tbtaco/Senior-Design/EAGLE/Batch 1/Button Board/Button Board Back.png

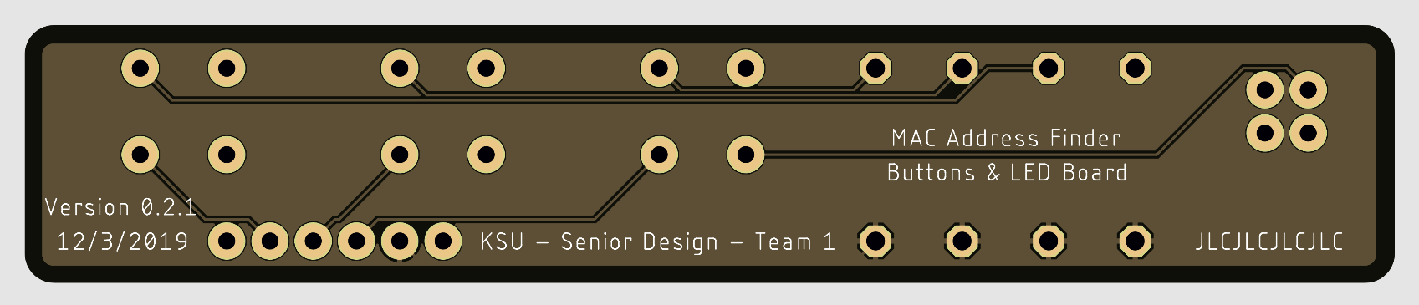
EAGLE/Batch 1/Button Board/Button Board Back.png
