tbtaco/Senior-Design/EAGLE/Batch 1/Button Board/Button Board BRD Dark.png

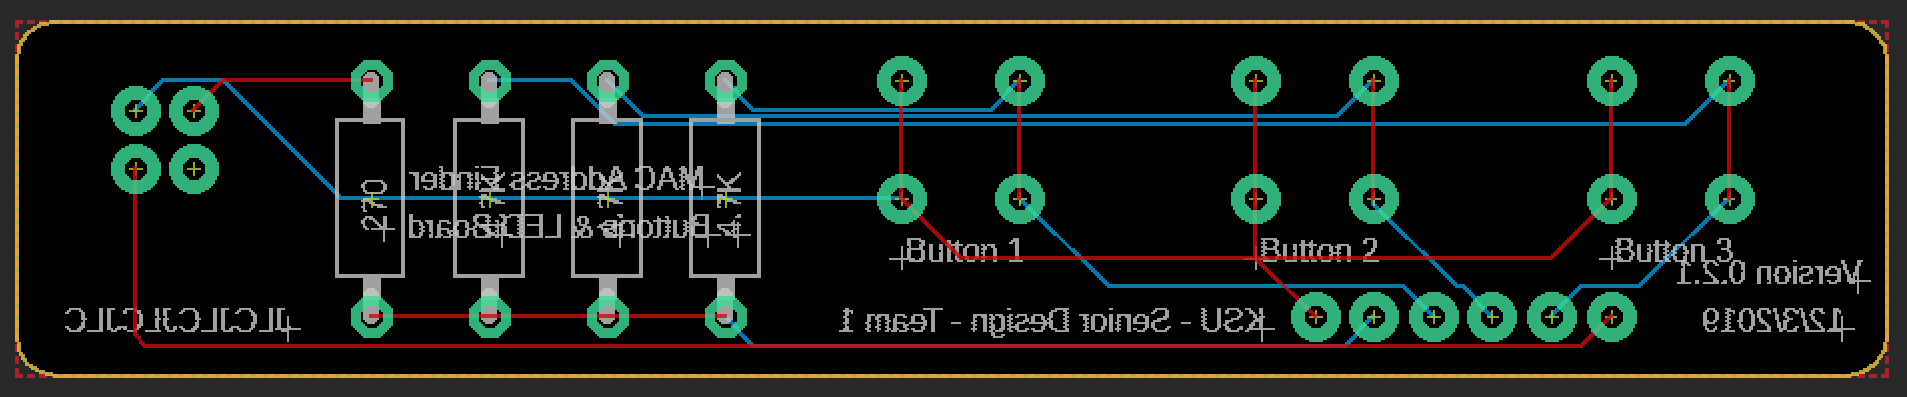
EAGLE/Batch 1/Button Board/Button Board BRD Dark.png
