tbtaco/Senior-Design/EAGLE/Batch 1/Button Board/Button Board BRD Light.png

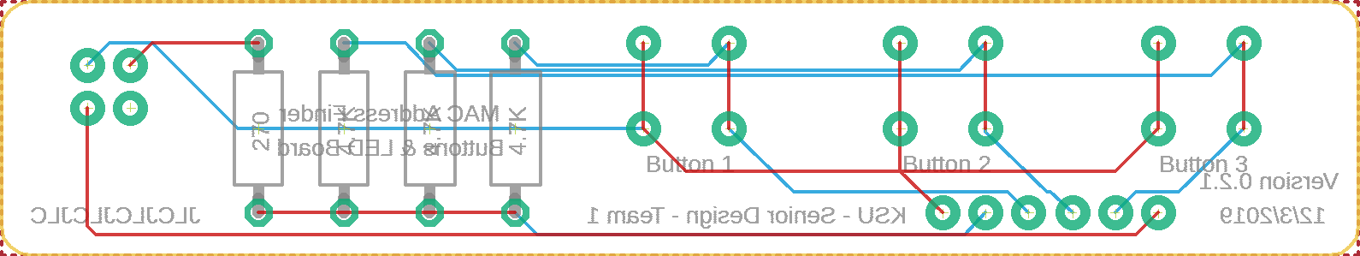
EAGLE/Batch 1/Button Board/Button Board BRD Light.png
