tbtaco/Senior-Design/EAGLE/Batch 1/Button Board/Button Board Built.JPG

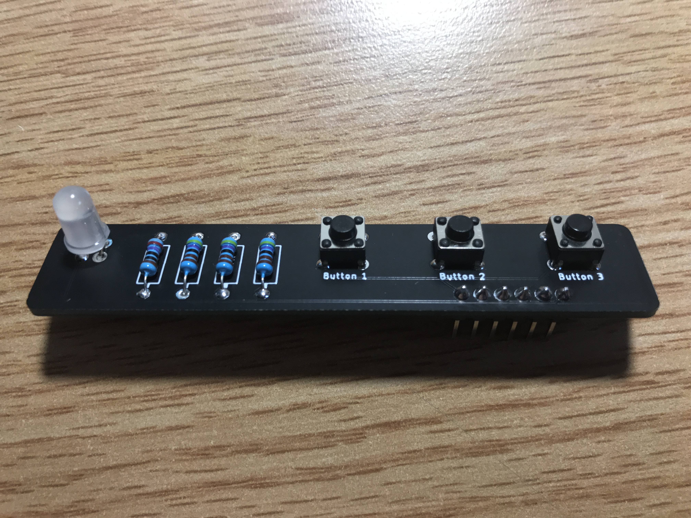
EAGLE/Batch 1/Button Board/Button Board Built.JPG
