tbtaco/Senior-Design/EAGLE/Batch 1/Button Board/Button Board Front.png

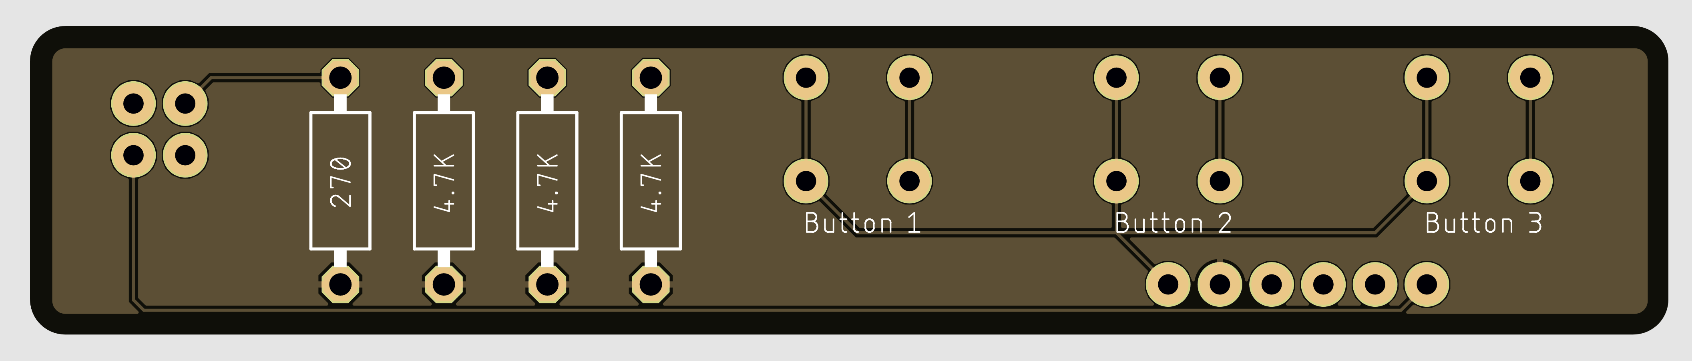
EAGLE/Batch 1/Button Board/Button Board Front.png
