tbtaco/Senior-Design/EAGLE/Batch 1/Firmware Update Board/Firmware Update Board Back.png

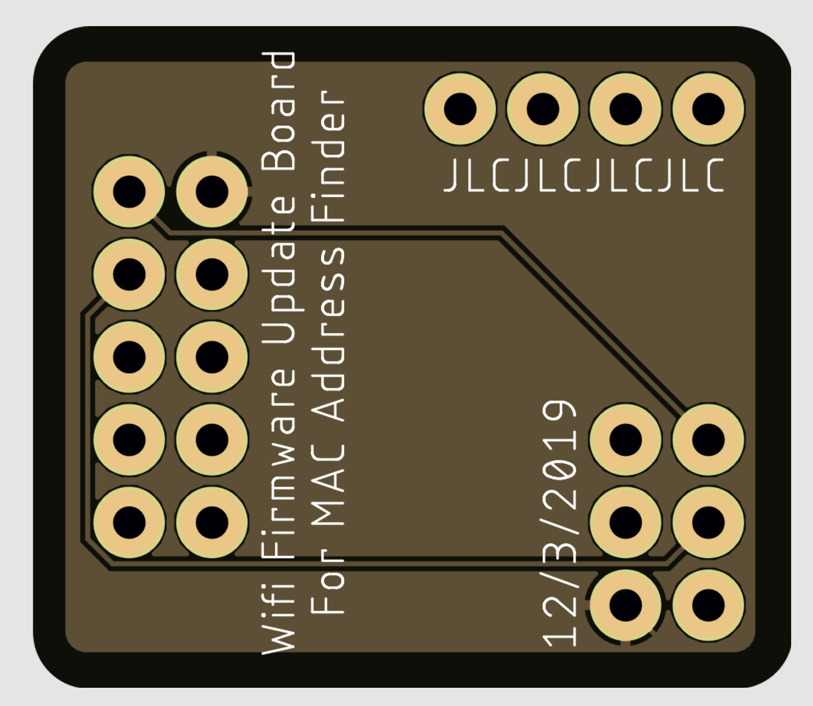
EAGLE/Batch 1/Firmware Update Board/Firmware Update Board Back.png
