tbtaco/Senior-Design/EAGLE/Batch 1/Firmware Update Board/Firmware Update Board Front.png

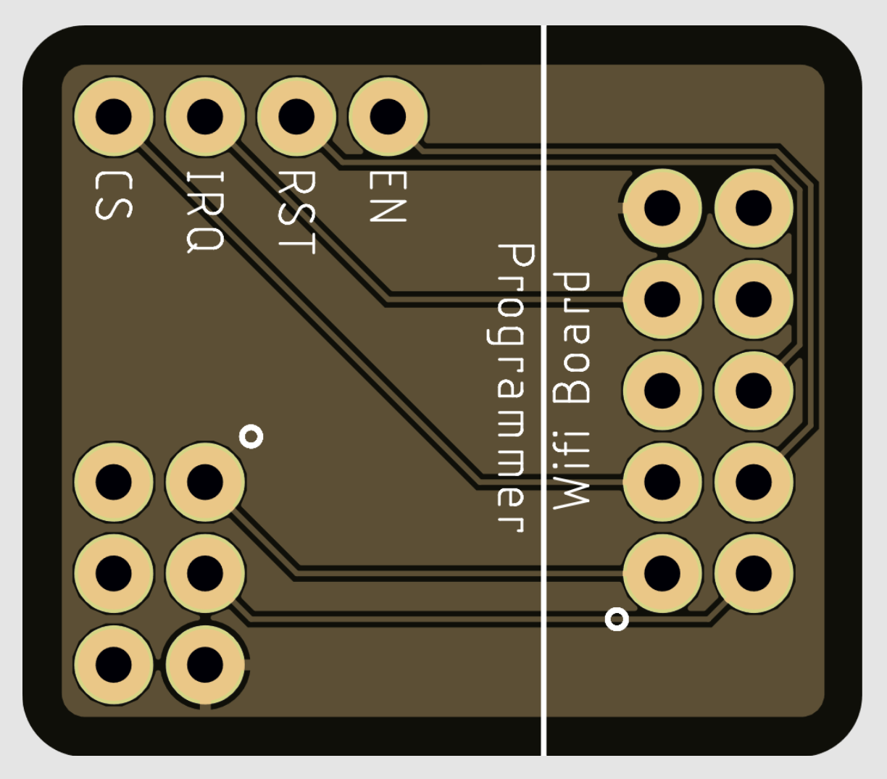
EAGLE/Batch 1/Firmware Update Board/Firmware Update Board Front.png
