tbtaco/Senior-Design/EAGLE/Batch 1/Firmware Update Board/Firmware Update Board Schematic.png

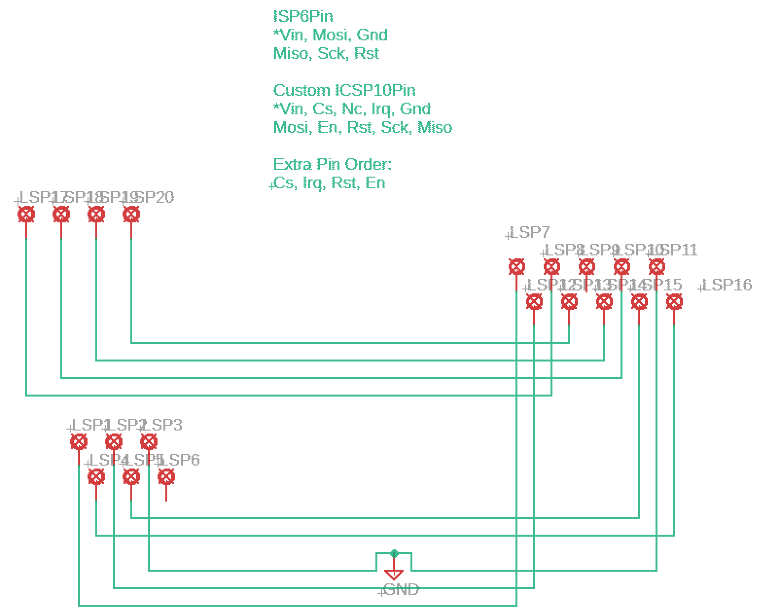
EAGLE/Batch 1/Firmware Update Board/Firmware Update Board Schematic.png
