tbtaco/Senior-Design/EAGLE/Batch 1/Main Board/Main Board Back Built.JPG

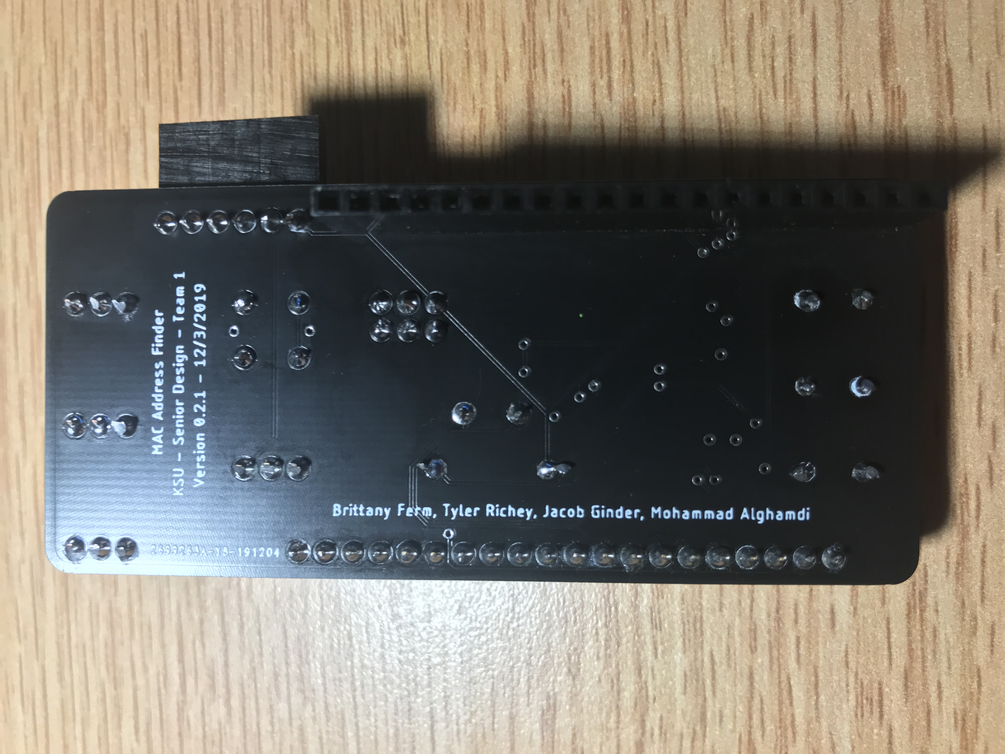
EAGLE/Batch 1/Main Board/Main Board Back Built.JPG
