tbtaco/Senior-Design/EAGLE/Batch 1/Main Board/Main Board Back.png

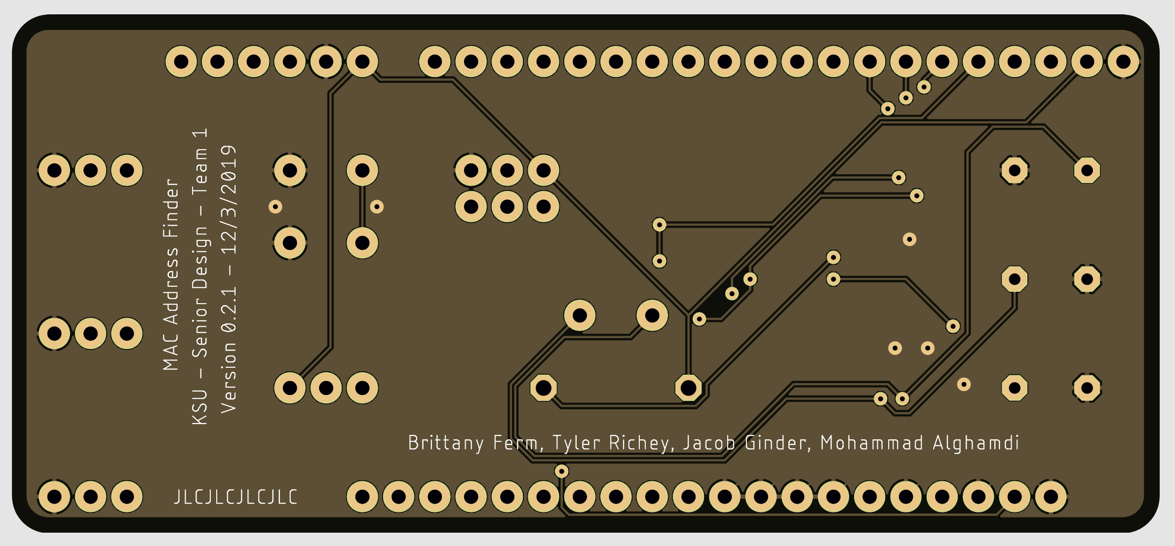
EAGLE/Batch 1/Main Board/Main Board Back.png
