tbtaco/Senior-Design/EAGLE/Batch 1/Main Board/Main Board BRD Dark.png

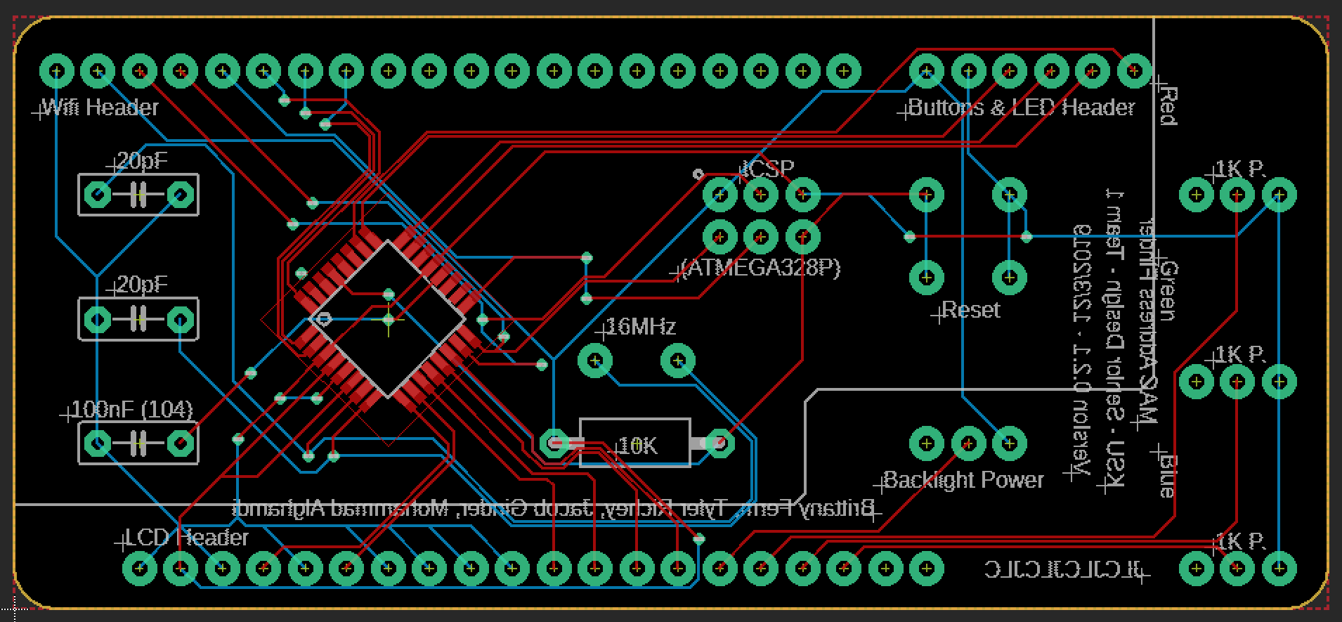
EAGLE/Batch 1/Main Board/Main Board BRD Dark.png
