tbtaco/Senior-Design/EAGLE/Batch 1/Main Board/Main Board BRD Light.png

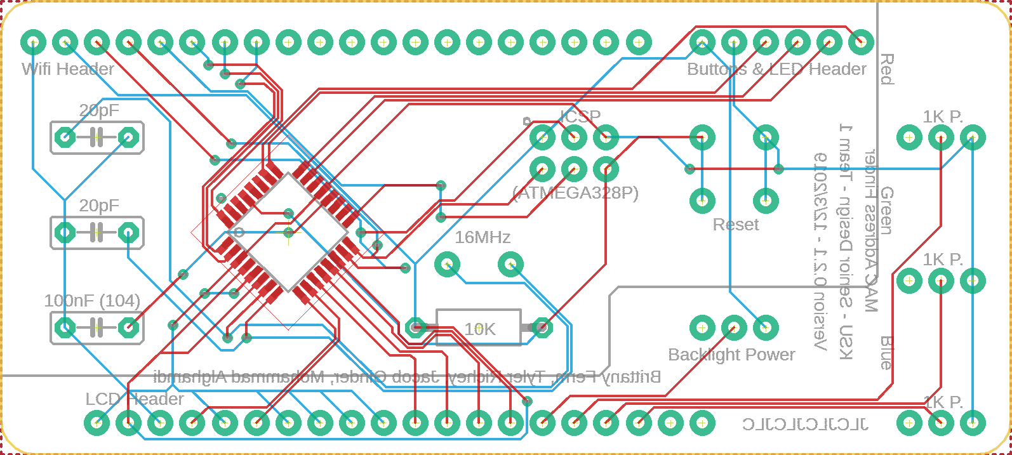
EAGLE/Batch 1/Main Board/Main Board BRD Light.png
