tbtaco/Senior-Design/EAGLE/Batch 1/Main Board/Main Board Front Built.JPG

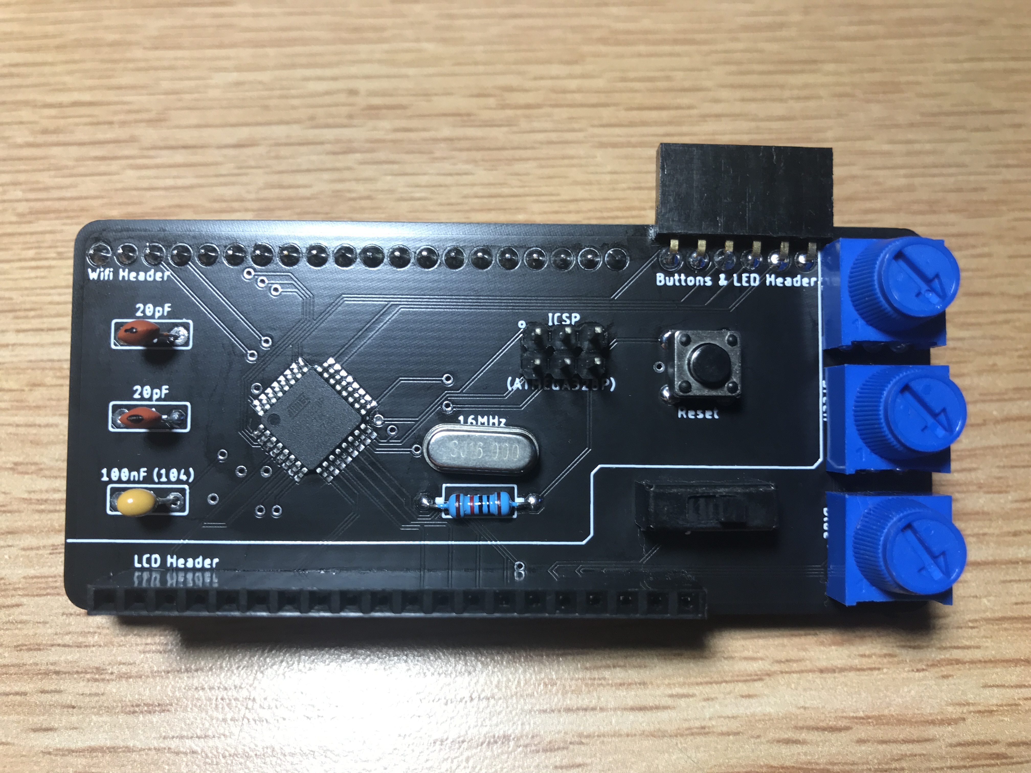
EAGLE/Batch 1/Main Board/Main Board Front Built.JPG
