tbtaco/Senior-Design/EAGLE/Batch 1/Main Board/Main Board Front.png

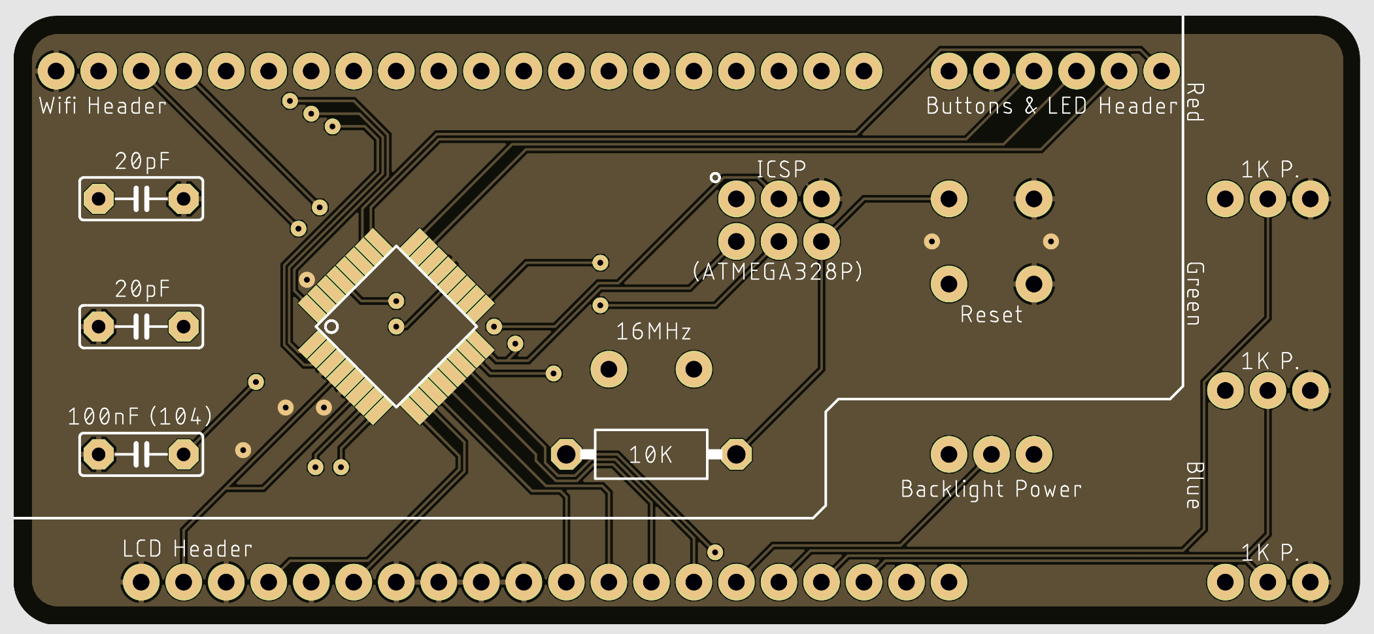
EAGLE/Batch 1/Main Board/Main Board Front.png
