tbtaco/Senior-Design/EAGLE/Batch 1/Main Board/Main Board Schematic.png

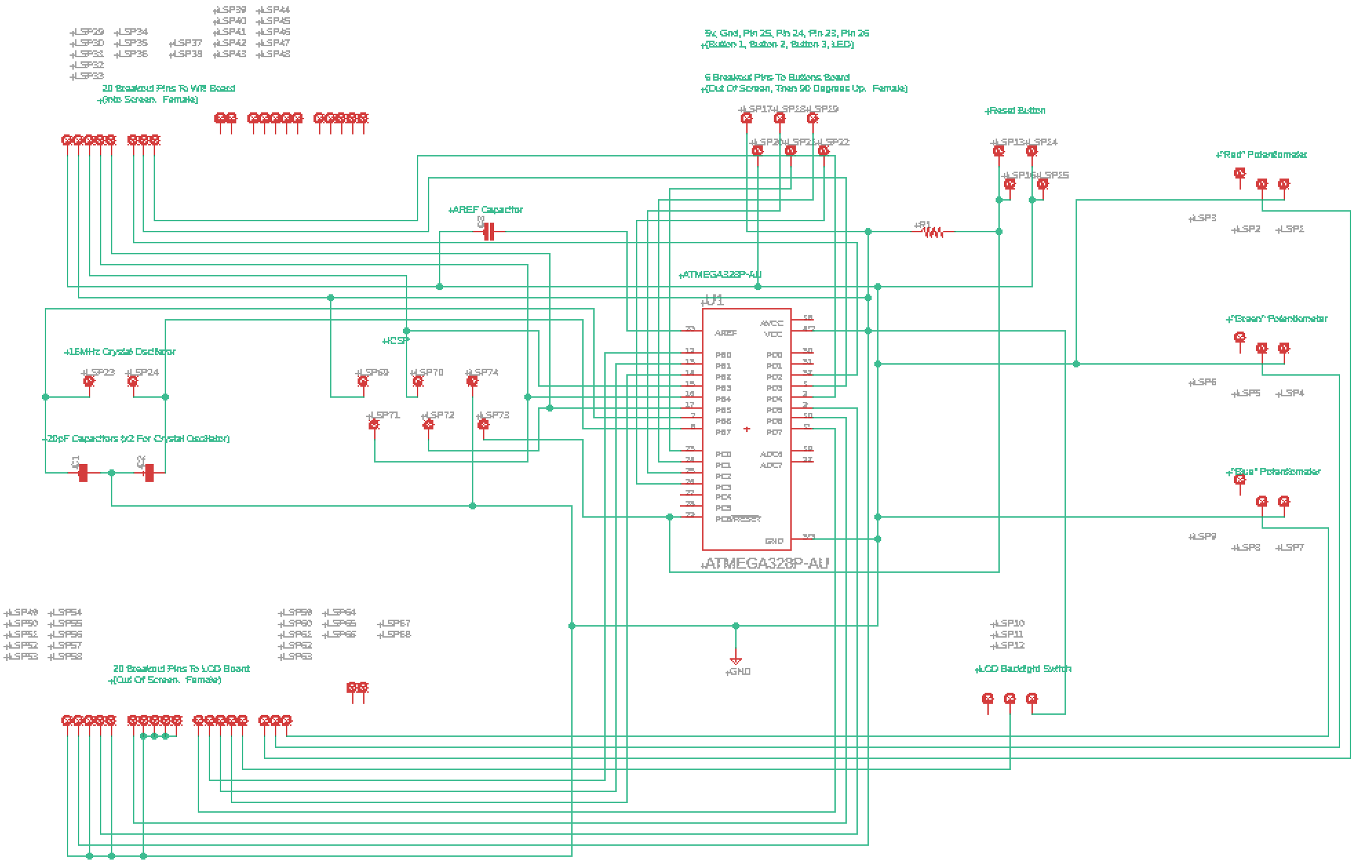
EAGLE/Batch 1/Main Board/Main Board Schematic.png
