tbtaco/Senior-Design/EAGLE/Batch 1/Programmer Board/Programmer Board Back.png

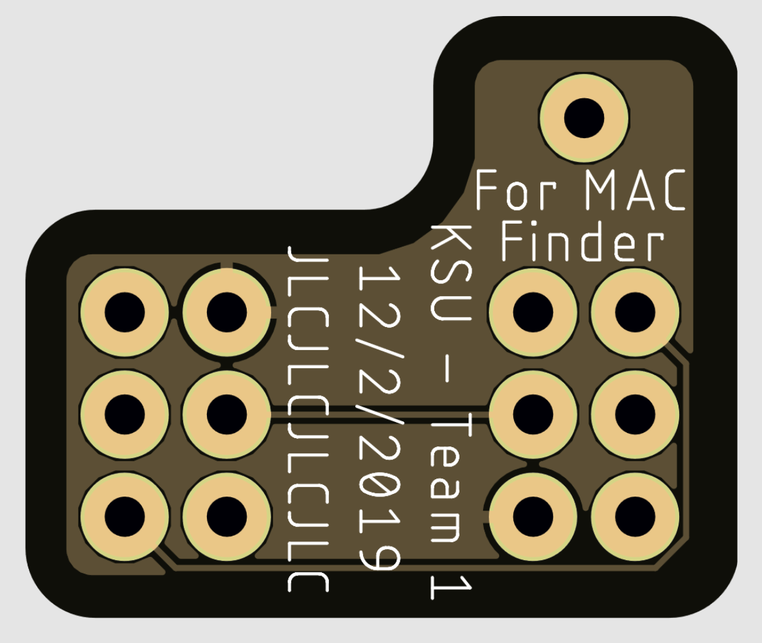
EAGLE/Batch 1/Programmer Board/Programmer Board Back.png
