tbtaco/Senior-Design/EAGLE/Batch 1/Programmer Board/Programmer Board BRD.png

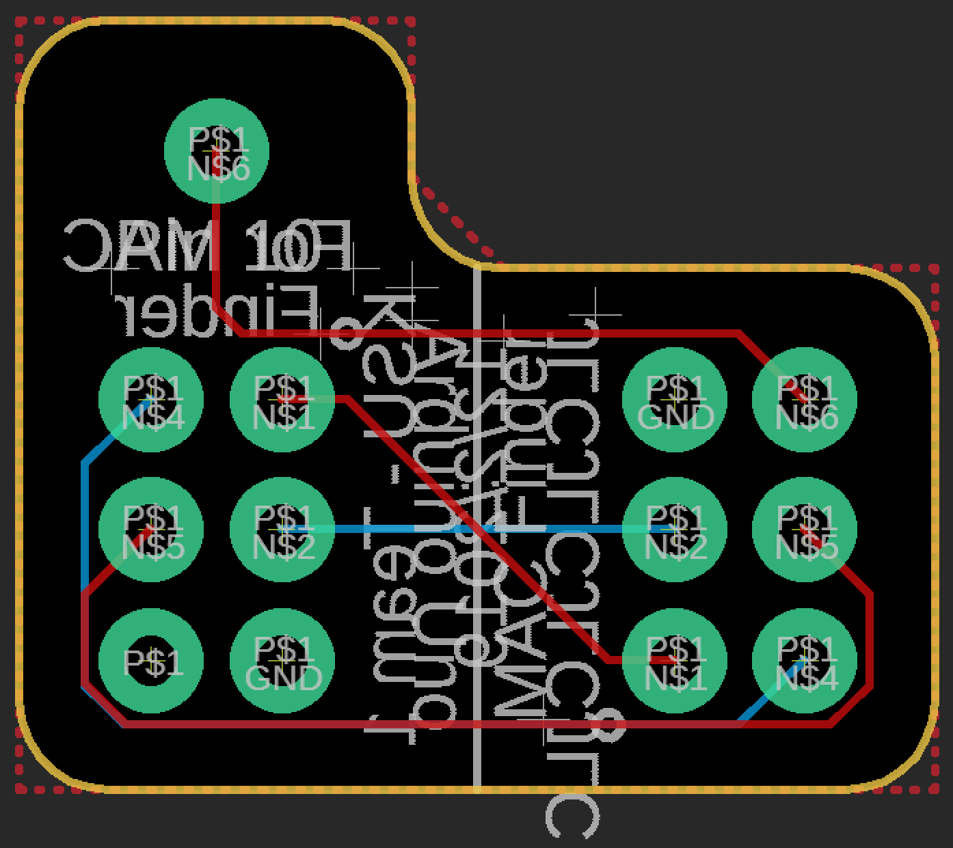
EAGLE/Batch 1/Programmer Board/Programmer Board BRD.png
