tbtaco/Senior-Design/EAGLE/Batch 1/Programmer Board/Programmer Board Front.png

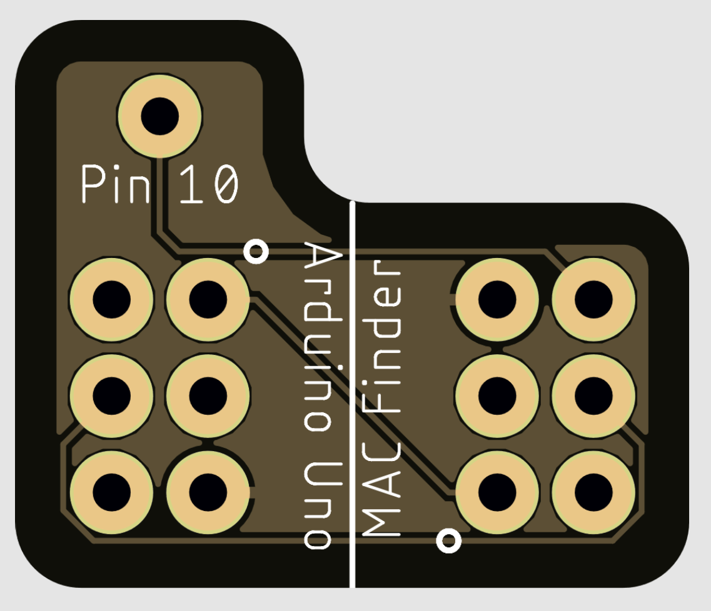
EAGLE/Batch 1/Programmer Board/Programmer Board Front.png
