tbtaco/Senior-Design/EAGLE/Batch 1/Wifi Board/Wifi Board Back.png

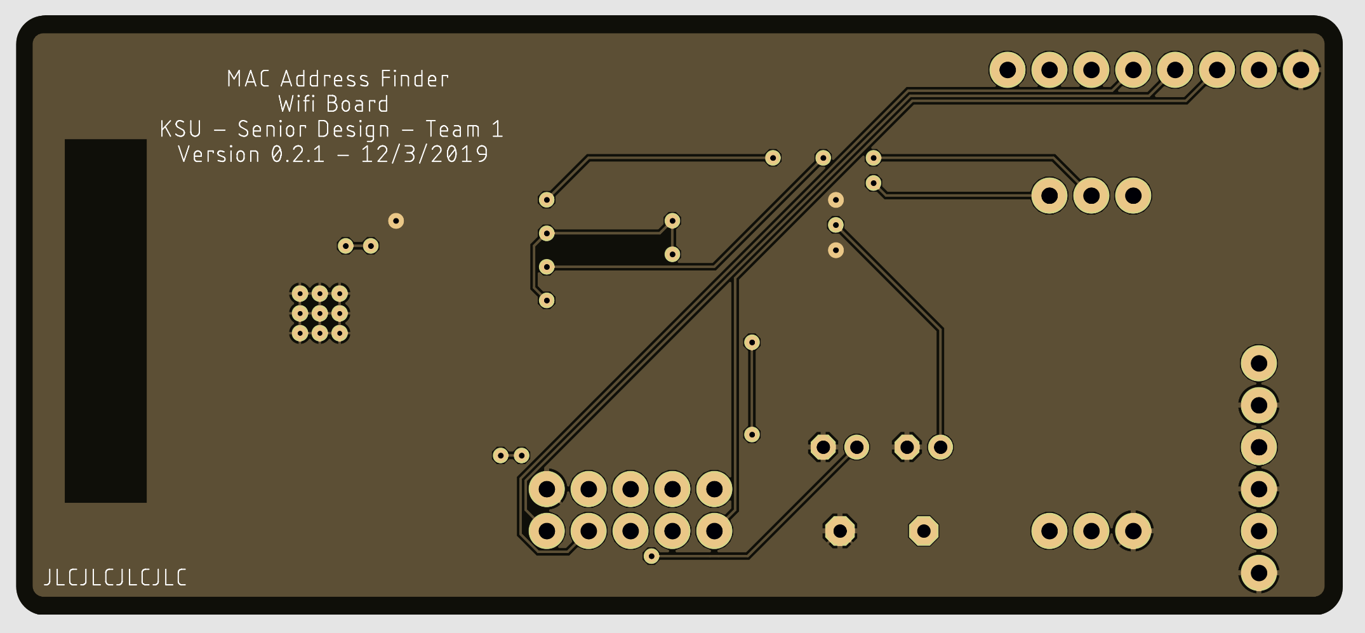
EAGLE/Batch 1/Wifi Board/Wifi Board Back.png
