tbtaco/Senior-Design/EAGLE/Batch 1/Wifi Board/Wifi Board BRD.png

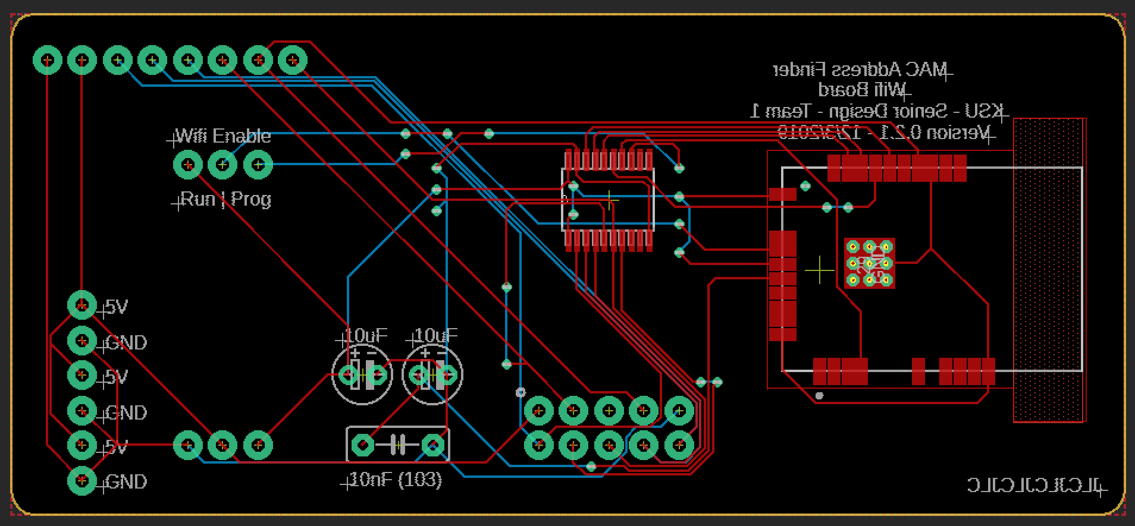
EAGLE/Batch 1/Wifi Board/Wifi Board BRD.png
