tbtaco/Senior-Design/EAGLE/Batch 1/Wifi Board/Wifi Board Built.JPG

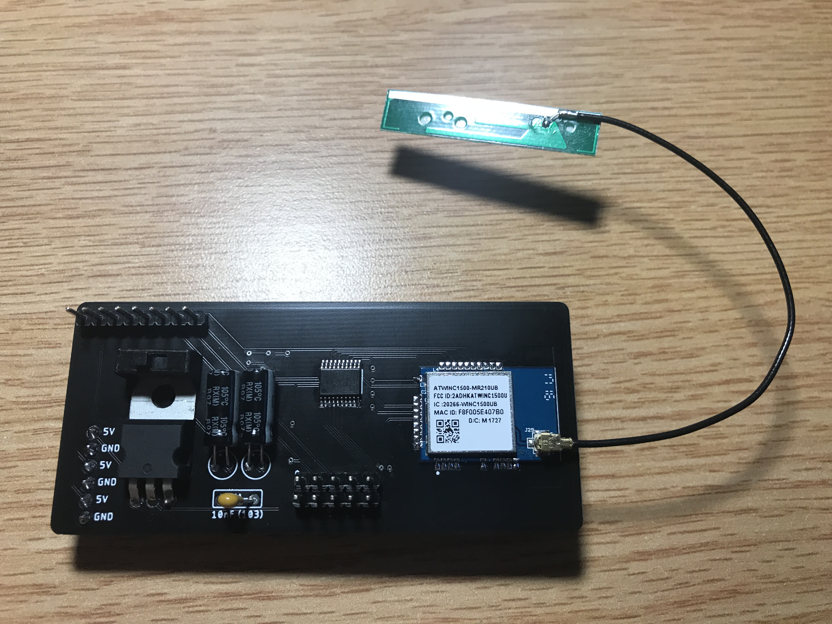
EAGLE/Batch 1/Wifi Board/Wifi Board Built.JPG
