tbtaco/Senior-Design/EAGLE/Batch 1/Wifi Board/Wifi Board Front.png

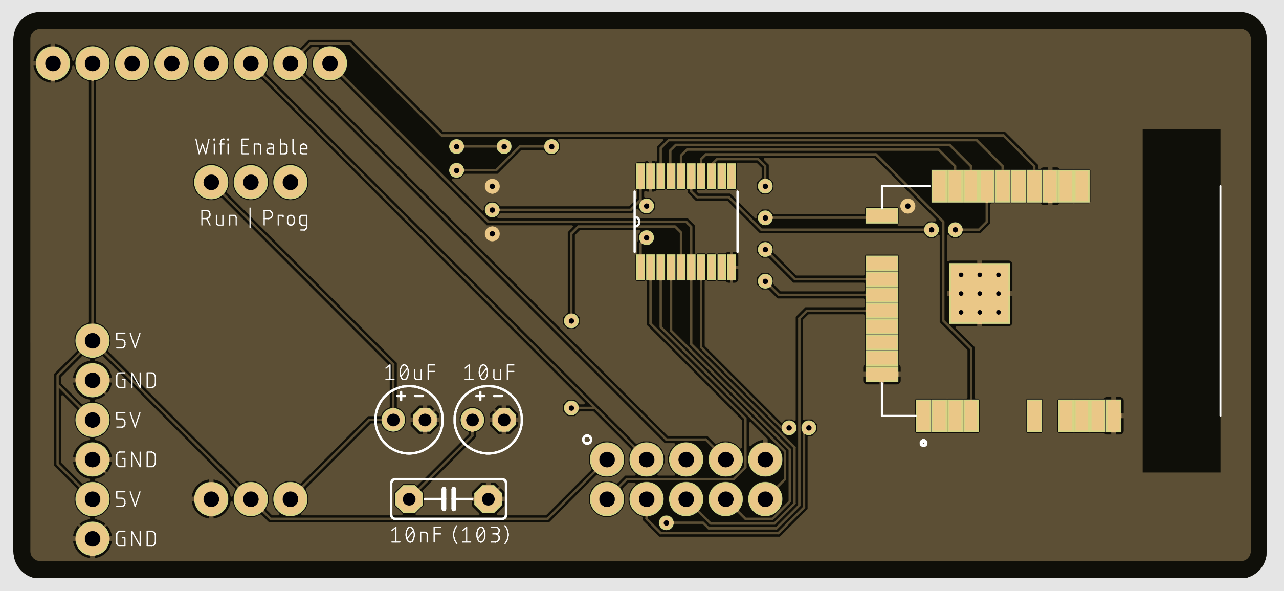
EAGLE/Batch 1/Wifi Board/Wifi Board Front.png
