tbtaco/Senior-Design/EAGLE/Batch 2/Octal Transceiver Breakout/Octal Transceiver Breakout Front.png

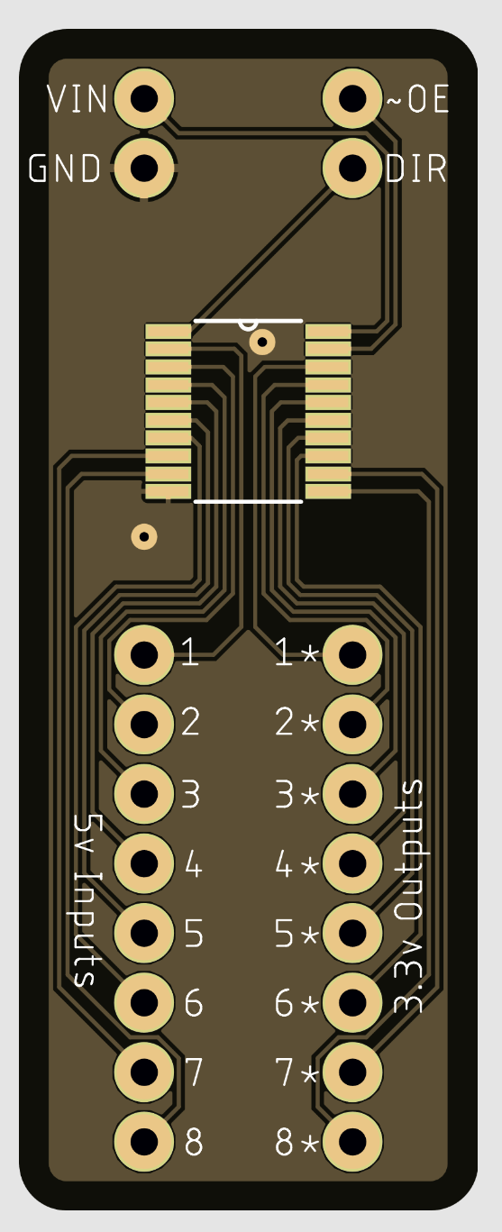
EAGLE/Batch 2/Octal Transceiver Breakout/Octal Transceiver Breakout Front.png
