tbtaco/Senior-Design/EAGLE/Batch 2/Programmer Board/Programmer Board Back.png

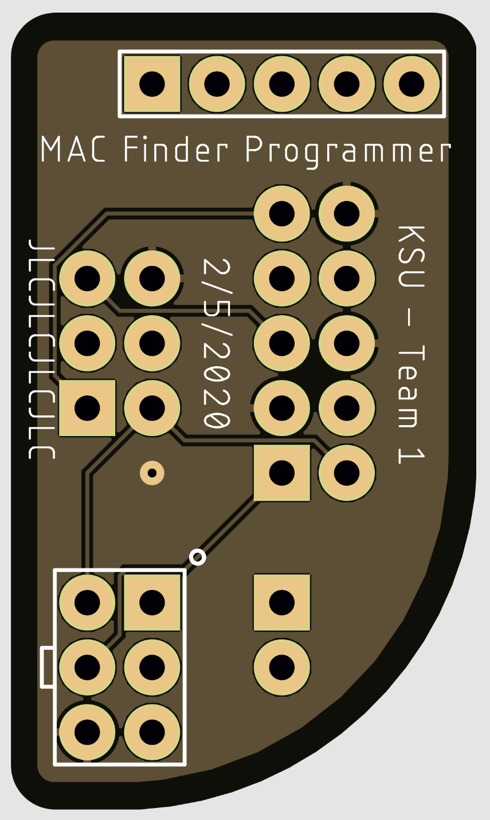
EAGLE/Batch 2/Programmer Board/Programmer Board Back.png
