tbtaco/Senior-Design/EAGLE/Batch 2/Programmer Board/Programmer Board BRD Dark.png

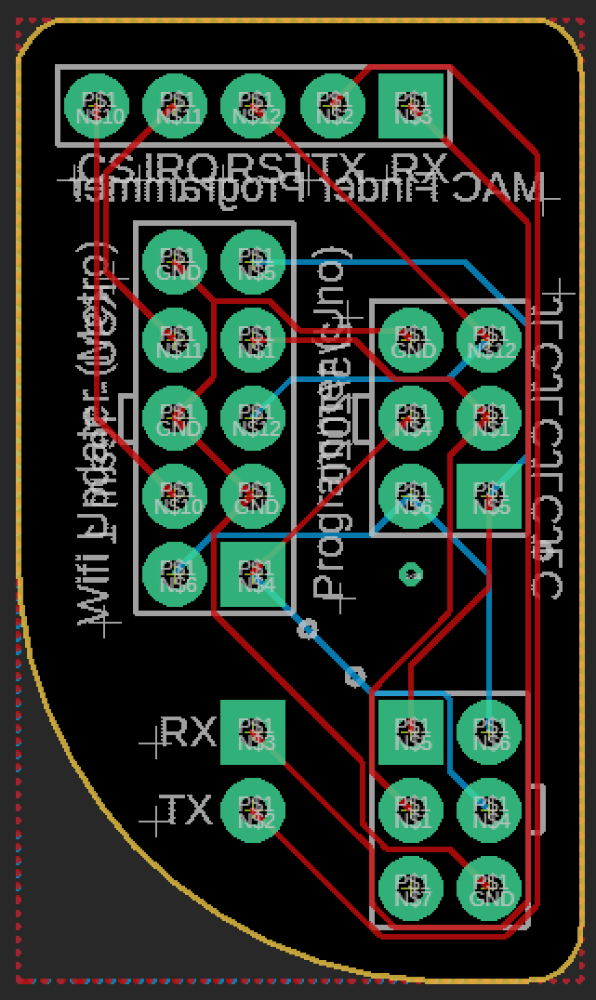
EAGLE/Batch 2/Programmer Board/Programmer Board BRD Dark.png
