tbtaco/Senior-Design/EAGLE/Batch 2/Programmer Board/Programmer Board BRD Light.png

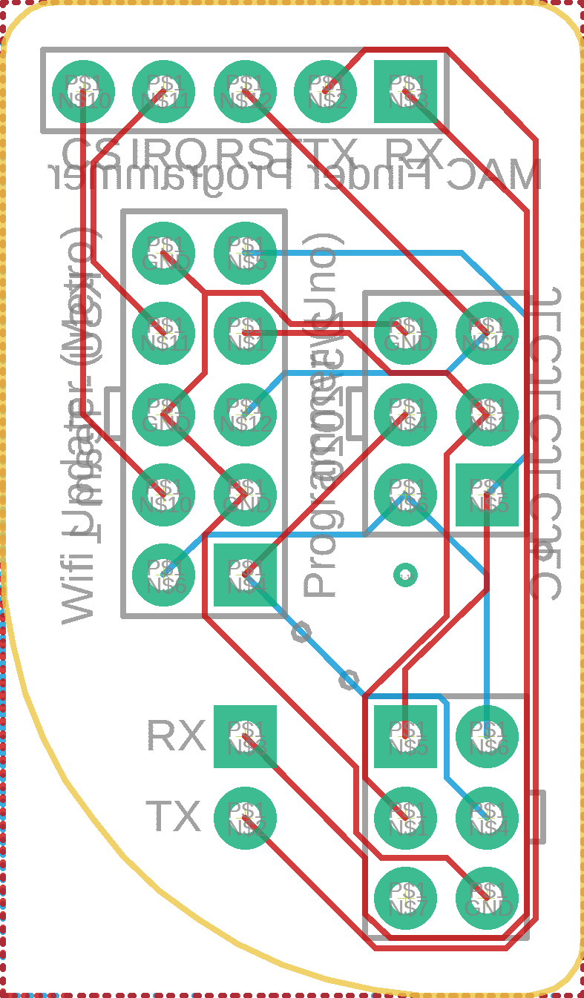
EAGLE/Batch 2/Programmer Board/Programmer Board BRD Light.png
