tbtaco/Senior-Design/EAGLE/Batch 2/Programmer Board/Programmer Board Built.jpg

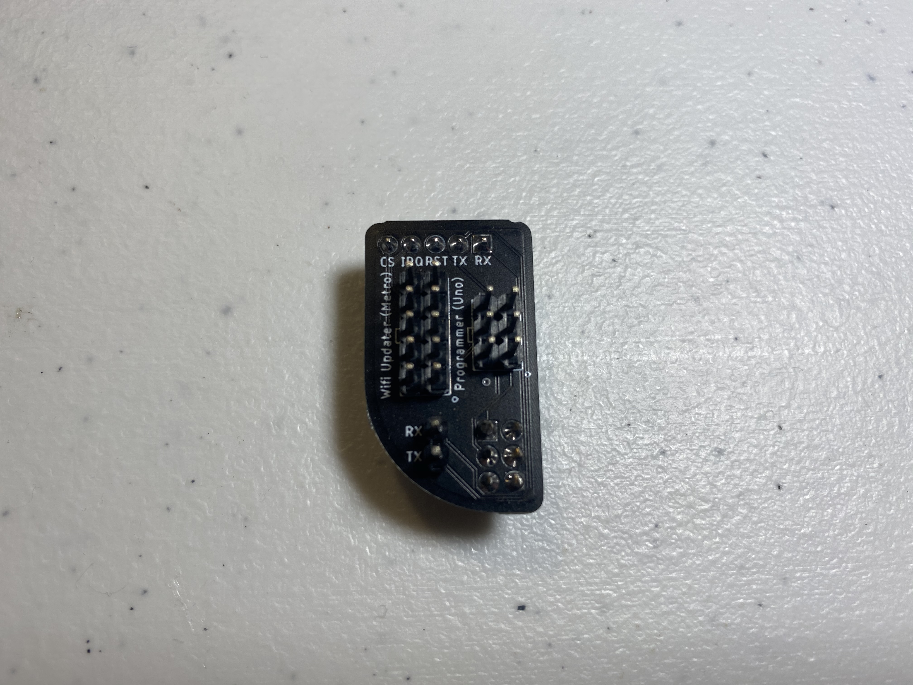
EAGLE/Batch 2/Programmer Board/Programmer Board Built.jpg
