tbtaco/Senior-Design/EAGLE/Batch 2/Programmer Board/Programmer Board Front.png

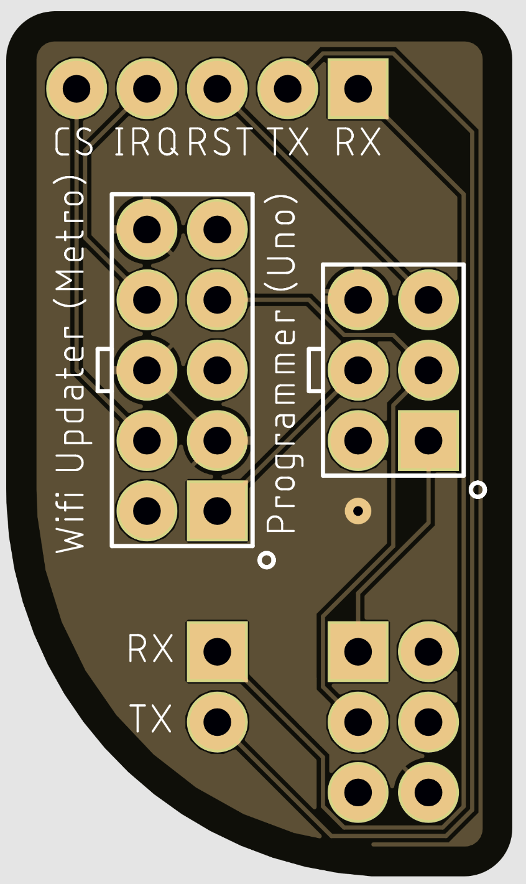
EAGLE/Batch 2/Programmer Board/Programmer Board Front.png
