tbtaco/Senior-Design/EAGLE/Batch 2/Programmer Board/Programmer Board On Arduino Uno.jpg

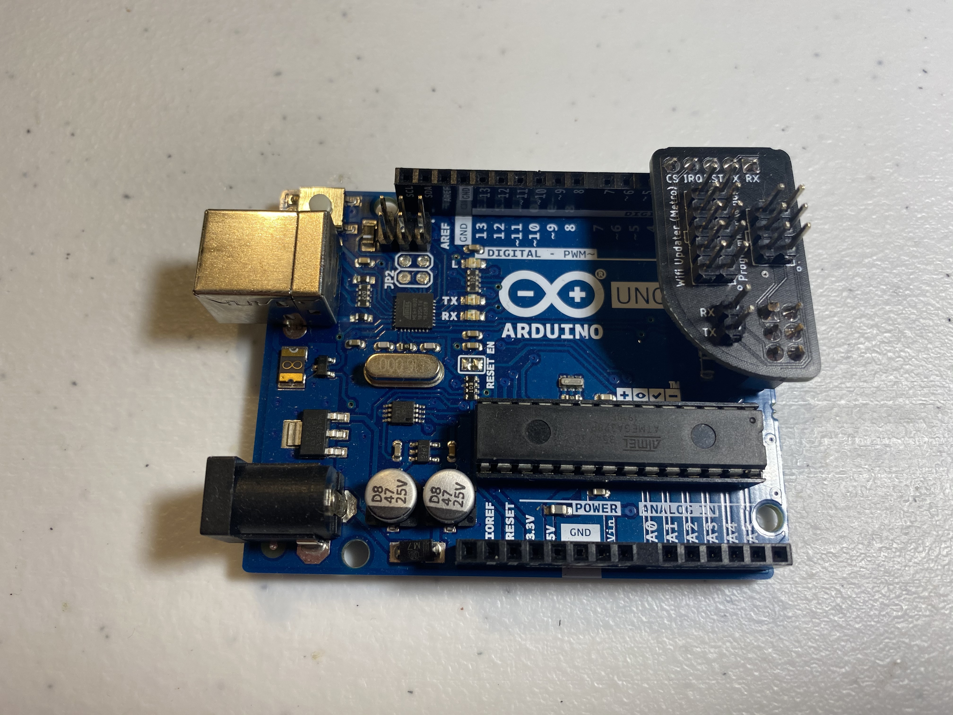
EAGLE/Batch 2/Programmer Board/Programmer Board On Arduino Uno.jpg
