tbtaco/Senior-Design/EAGLE/Batch 2/Programmer Board/Programmer Board Schematic.png

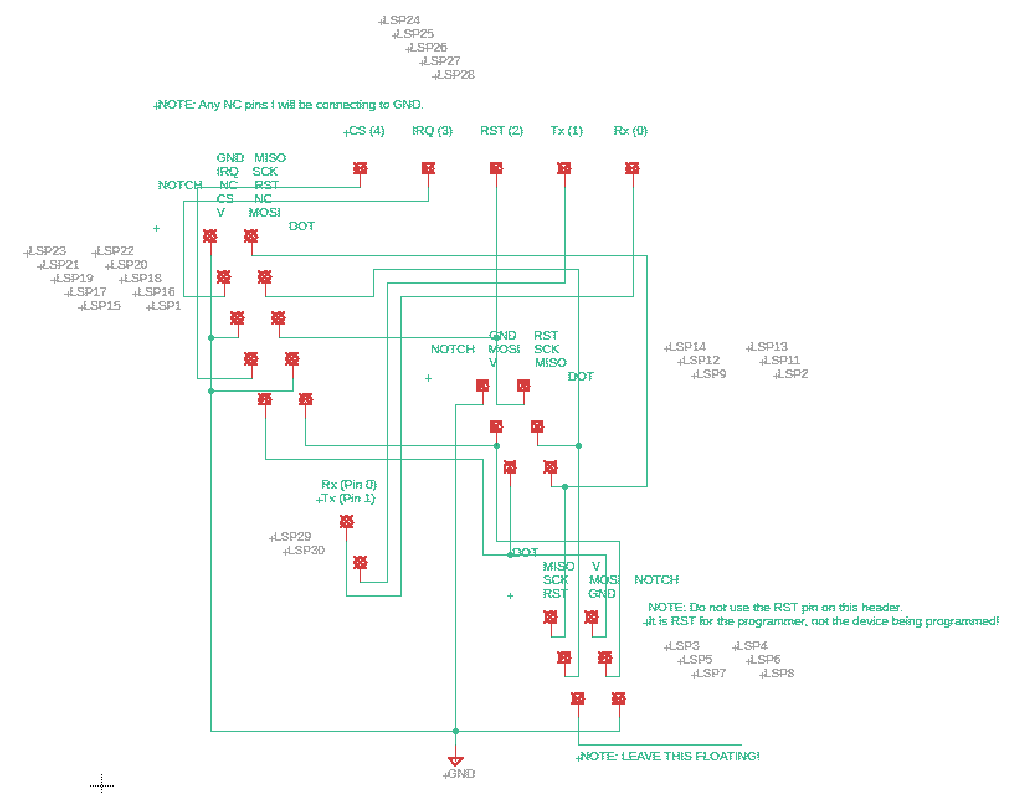
EAGLE/Batch 2/Programmer Board/Programmer Board Schematic.png
