tbtaco/Senior-Design/EAGLE/Batch 2/Wifi Module Breakout/Wifi Module Breakout BRD.png

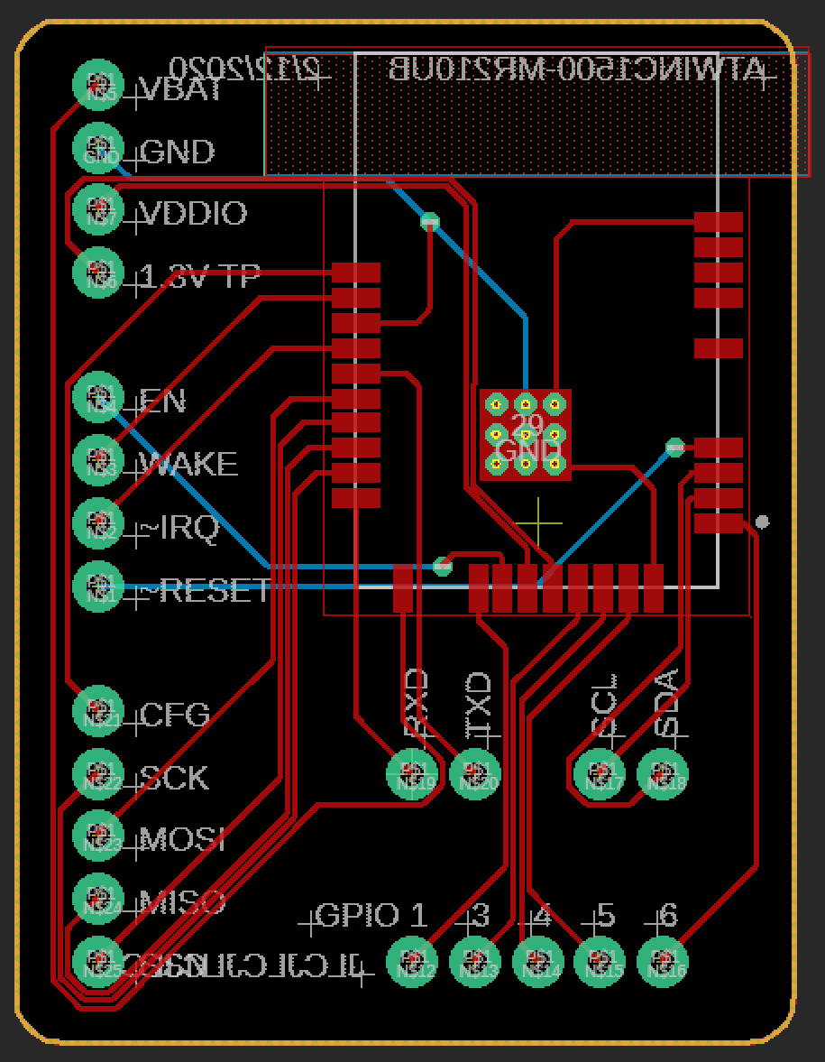
EAGLE/Batch 2/Wifi Module Breakout/Wifi Module Breakout BRD.png
