tbtaco/Senior-Design/EAGLE/Batch 2/Wifi Module Breakout/Wifi Module Breakout Front.png

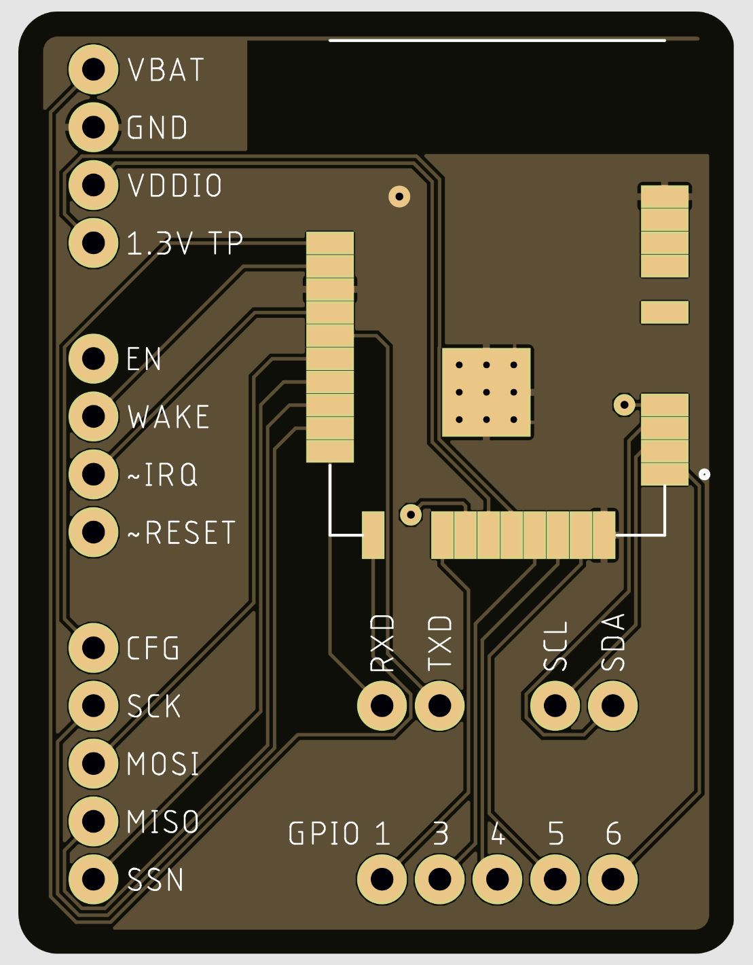
EAGLE/Batch 2/Wifi Module Breakout/Wifi Module Breakout Front.png
