tbtaco/Senior-Design/EAGLE/Batch 3/Wifi Board Rework/Wifi Board Rework Back.png

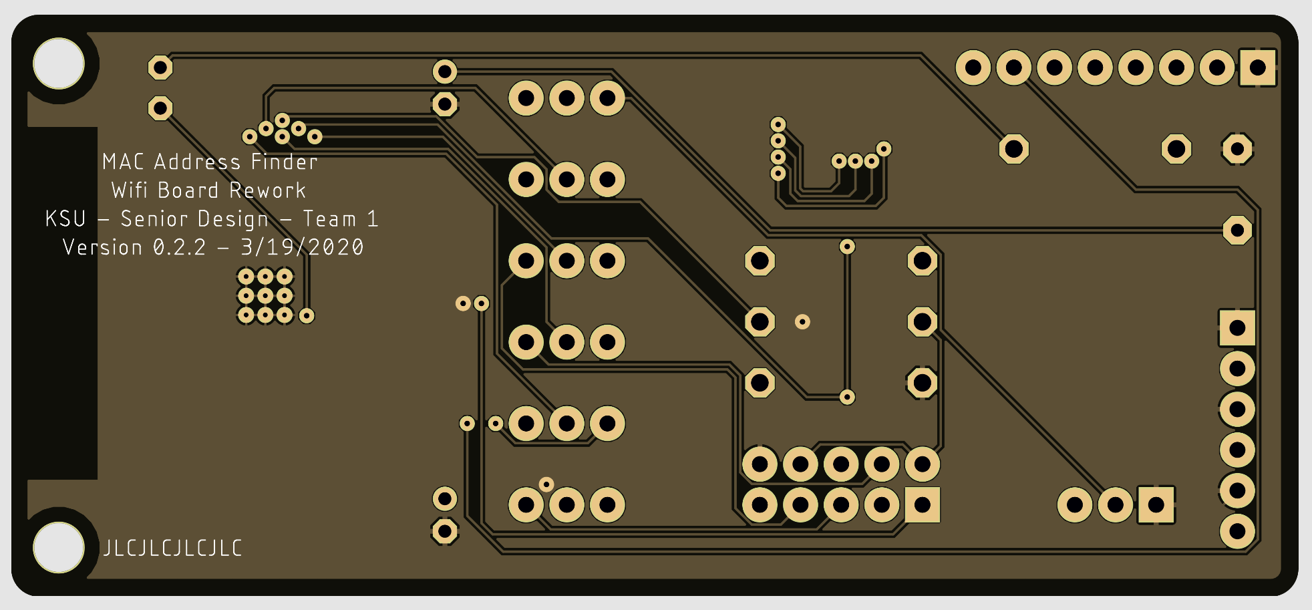
EAGLE/Batch 3/Wifi Board Rework/Wifi Board Rework Back.png
