tbtaco/Senior-Design/EAGLE/Batch 3/Wifi Board Rework/Wifi Board Rework BRD Light.png

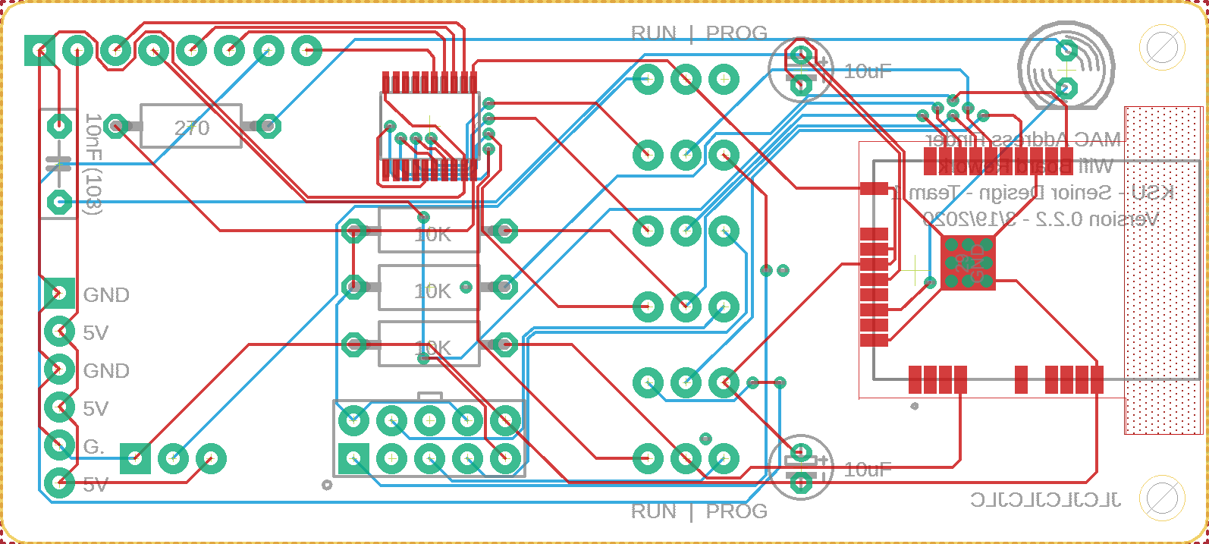
EAGLE/Batch 3/Wifi Board Rework/Wifi Board Rework BRD Light.png
