tbtaco/Senior-Design/EAGLE/Batch 3/Wifi Board Rework/Wifi Board Rework Built.jpg

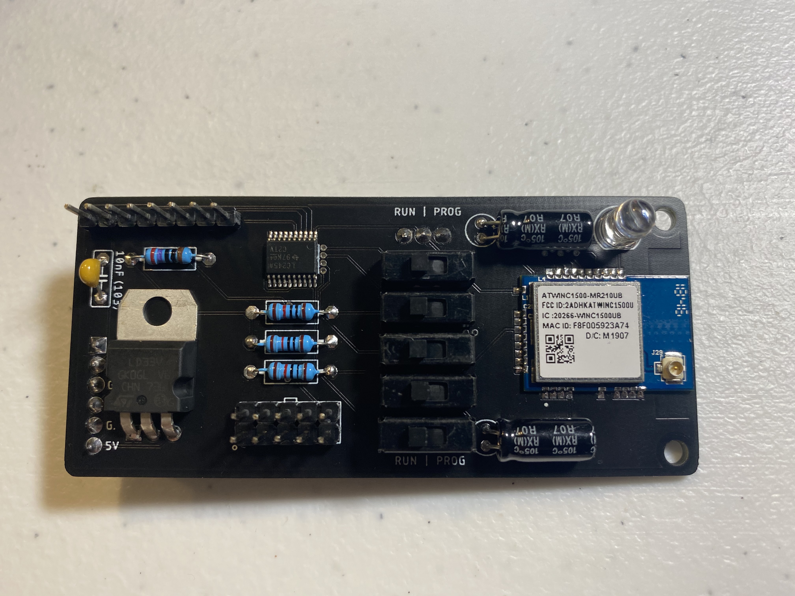
EAGLE/Batch 3/Wifi Board Rework/Wifi Board Rework Built.jpg
