tbtaco/Senior-Design/EAGLE/Batch 3/Wifi Board Rework/Wifi Board Rework Front.png

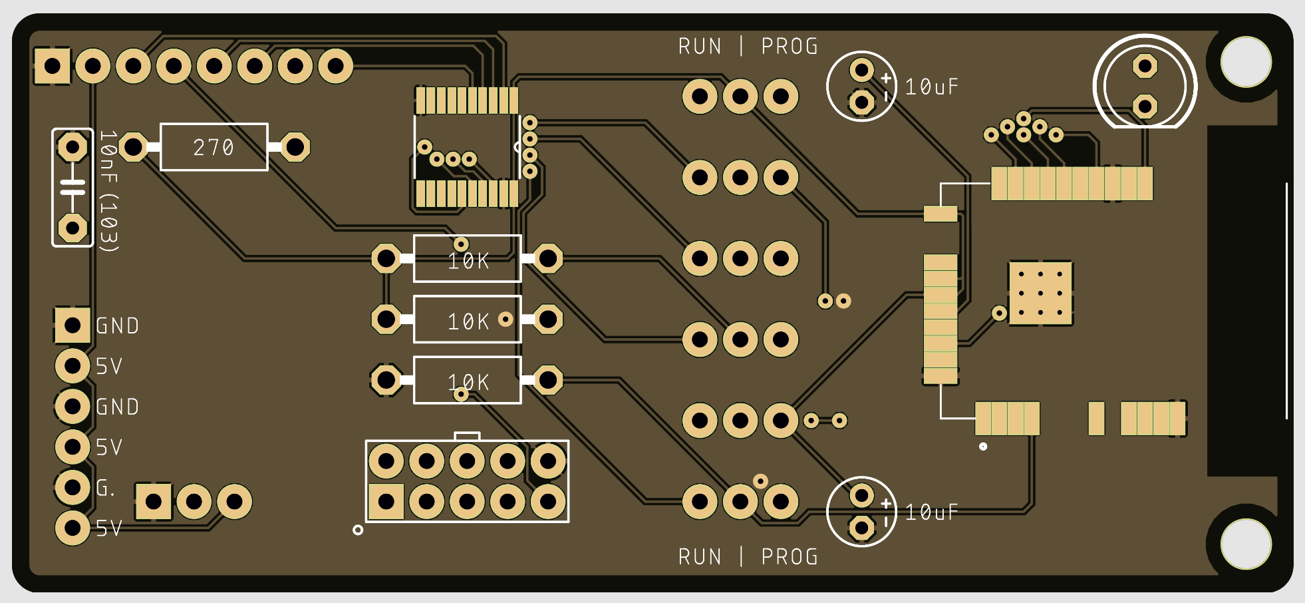
EAGLE/Batch 3/Wifi Board Rework/Wifi Board Rework Front.png
