tbtaco/Senior-Design/EAGLE/Batch 3/Wifi Board Rework/Wifi Board Rework Schematic.png

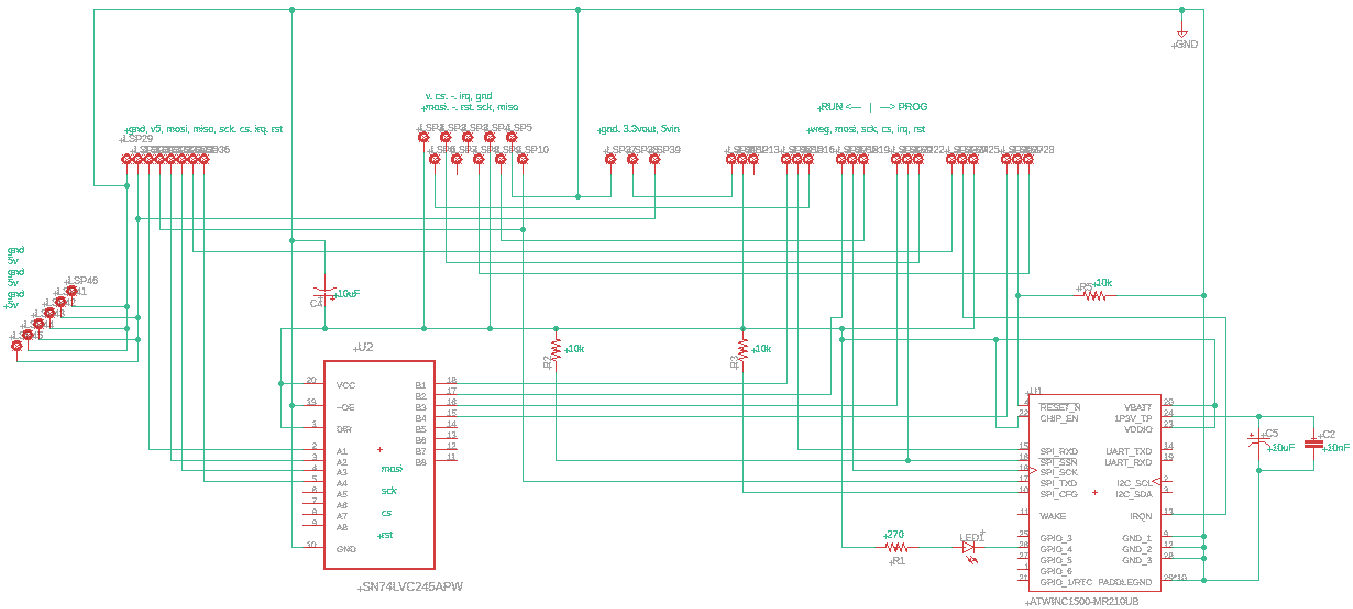
EAGLE/Batch 3/Wifi Board Rework/Wifi Board Rework Schematic.png
