tbtaco/Senior-Design/Other Resources/3D Render 1.jpg

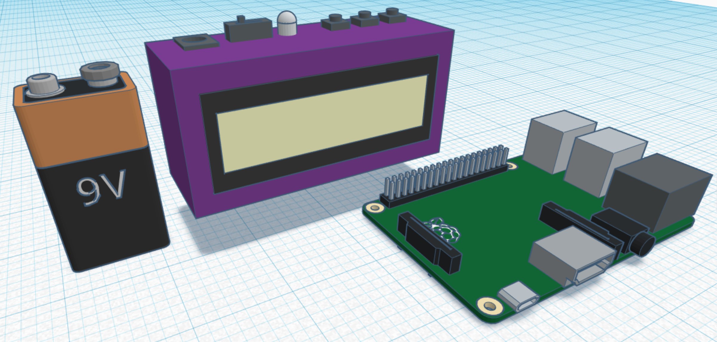
Other Resources/3D Render 1.jpg
