tbtaco/Senior-Design/Other Resources/3D Render 2.png

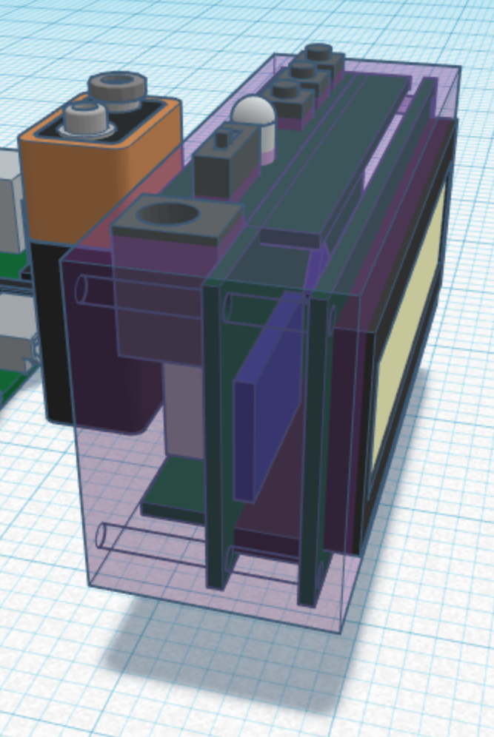
Other Resources/3D Render 2.png
