tbtaco/Senior-Design/Other Resources/Final.png

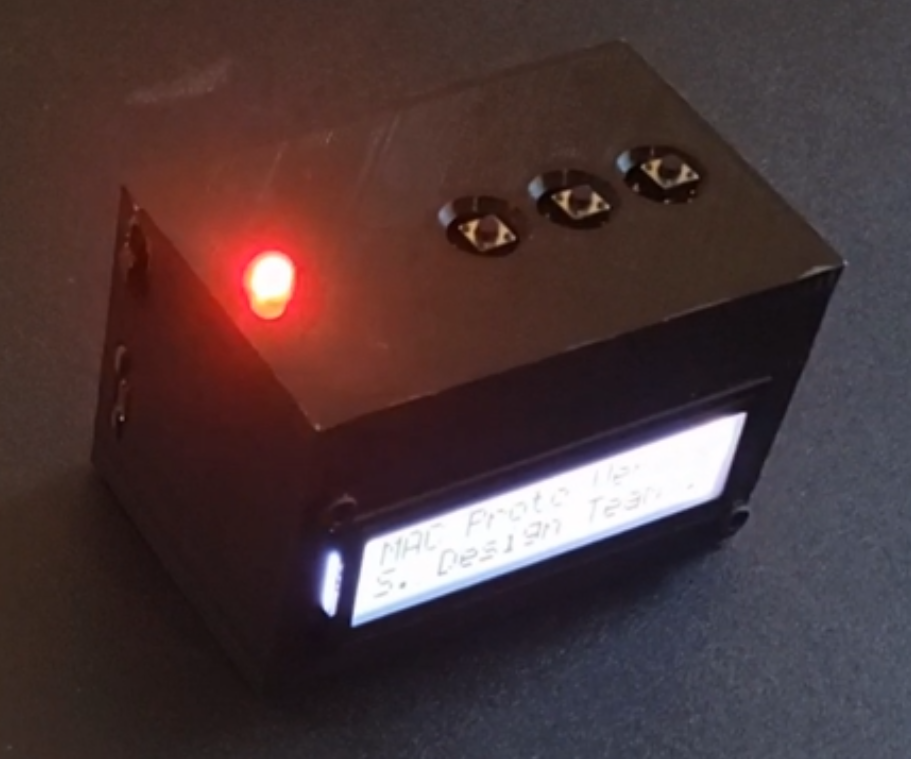
Other Resources/Final.png
