tbtaco/Senior-Design/Other Resources/Programming Main Board.jpg

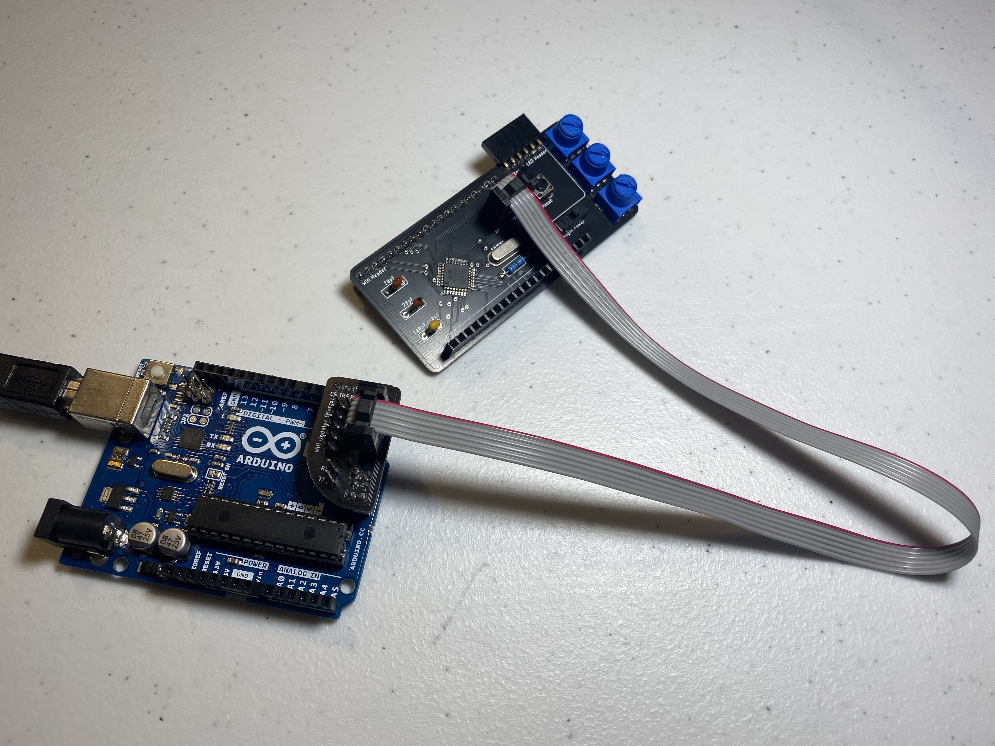
Other Resources/Programming Main Board.jpg
