tbtaco/Senior-Design/Other Resources/Programming Wifi Board.jpg

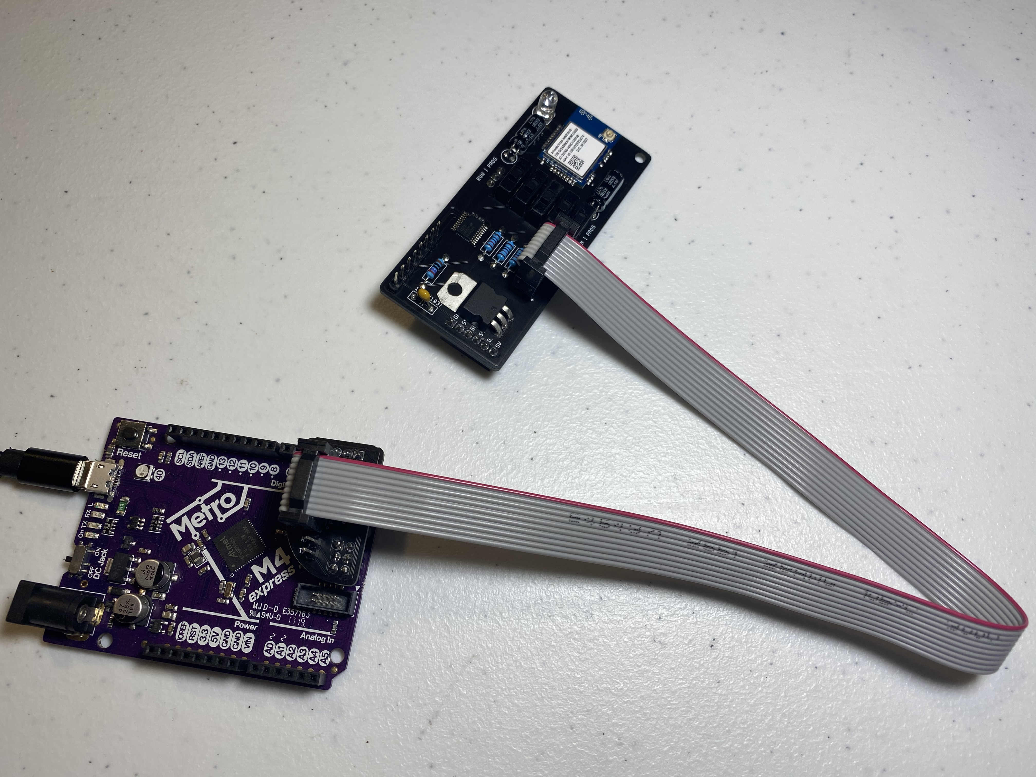
Other Resources/Programming Wifi Board.jpg
