tbtaco/Senior-Design/Other Resources/Proto 1 Next To Proto 2.JPG

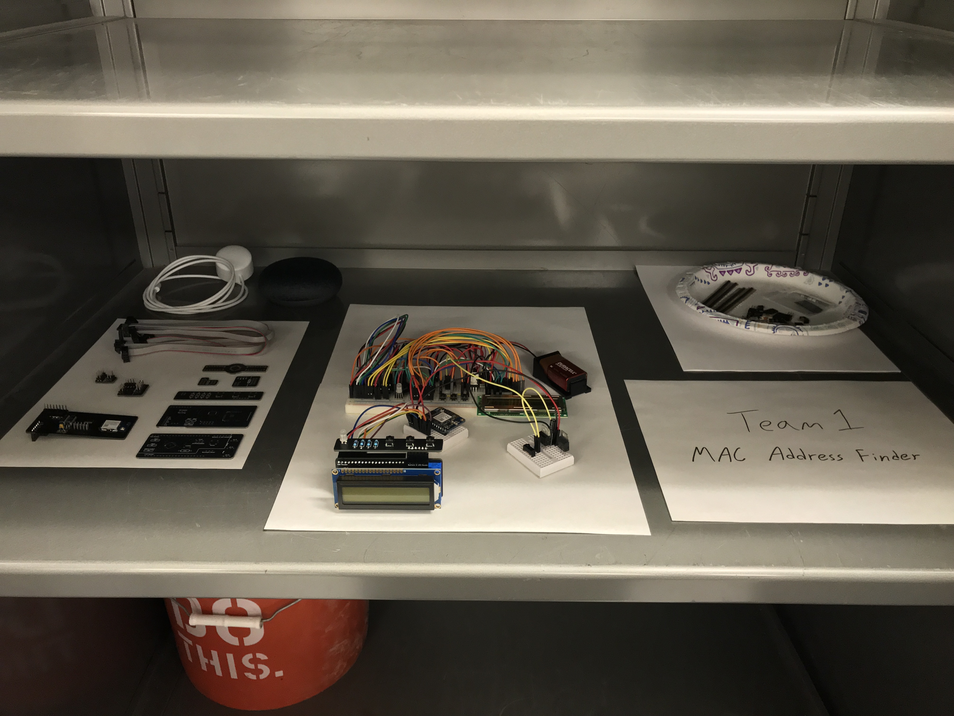
Other Resources/Proto 1 Next To Proto 2.JPG
