tbtaco/Senior-Design/Other Resources/Proto 2 Awesome Picture.JPG

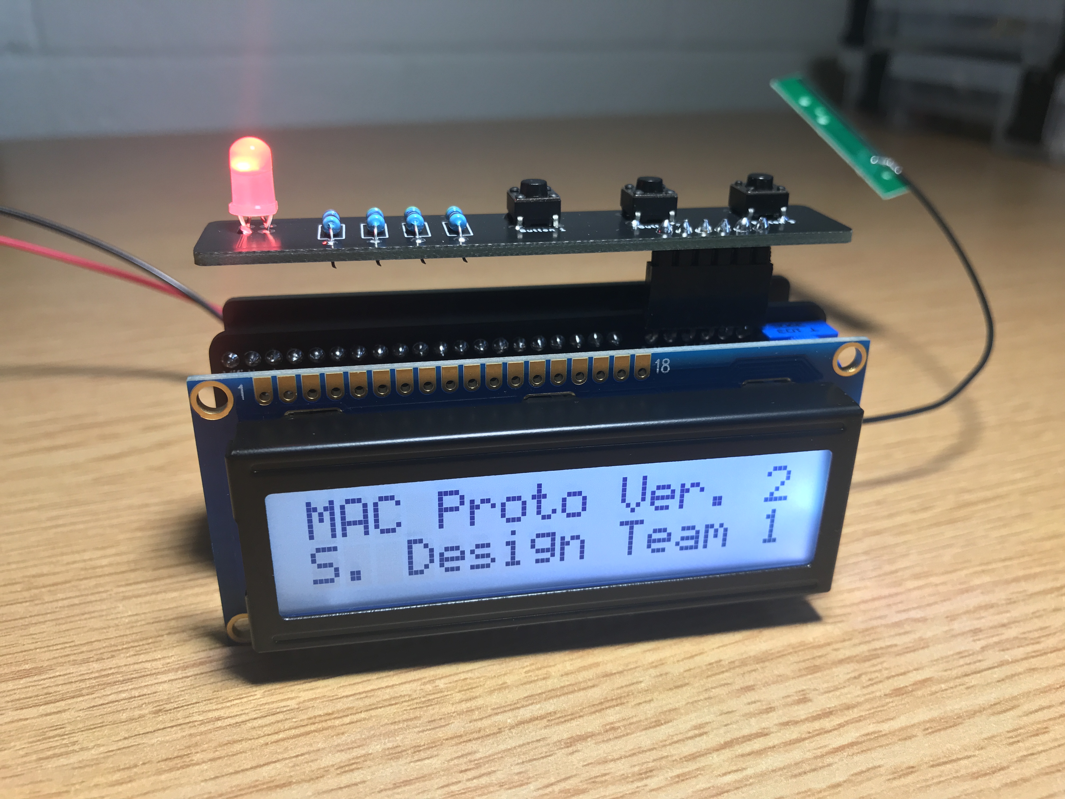
Other Resources/Proto 2 Awesome Picture.JPG
