tbtaco/Senior-Design/Other Resources/Proto 2.JPG

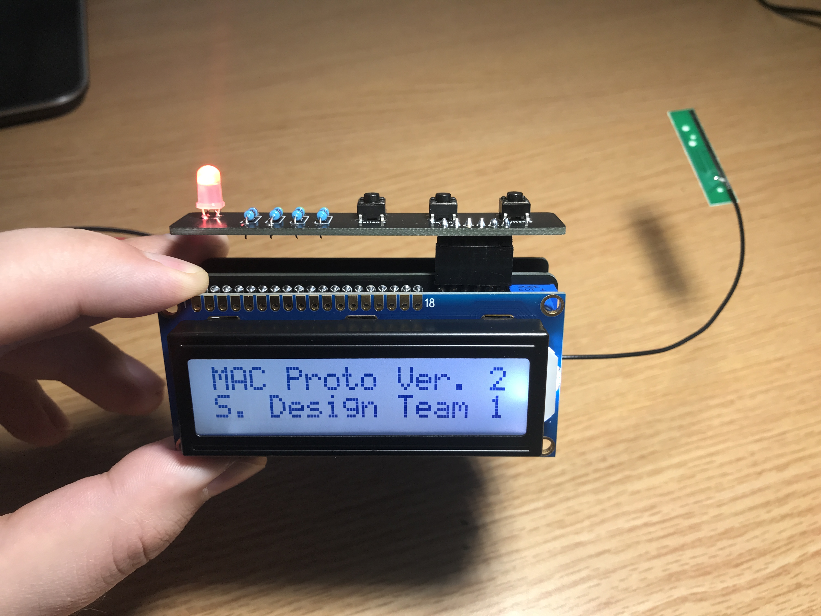
Other Resources/Proto 2.JPG
