tbtaco/Senior-Design/Arduino/MAC_Address_Finder_FirmwareUpdater/MAC_Address_Finder_FirmwareUpdater.ino

/*
 * MAC Address Finder Edited FirmwareUpdater Program
 * This program should be uploaded to an Adafruit Metro M4 and is used to update the firmware on the Wi-Fi module (WINC1500) on the MAC Address Finder Wi-Fi Board.
 * Any questions can be sent to Tyler Richey at tyler777@ksu.edu or tbtaco@hotmail.com
 */

/*
  FirmwareUpdate.h - Firmware Updater for WiFi101 / WINC1500.
  Copyright (c) 2015 Arduino LLC.  All right reserved.

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
  You should have received a copy of the GNU Lesser General Public
  License along with this library; if not, write to the Free Software
  Foundation, Inc., 51 Franklin St, Fifth Floor, Boston, MA  02110-1301  USA
*/

#include <WiFi101.h>
#include <spi_flash/include/spi_flash.h>

typedef struct __attribute__((__packed__)) {
  uint8_t command;
  uint32_t address;
  uint32_t arg1;
  uint16_t payloadLength;

  // payloadLenght bytes of data follows...
} UartPacket;

static const int MAX_PAYLOAD_SIZE = 1024;

#define CMD_READ_FLASH        0x01
#define CMD_WRITE_FLASH       0x02
#define CMD_ERASE_FLASH       0x03
#define CMD_MAX_PAYLOAD_SIZE  0x50
#define CMD_HELLO             0x99

void setup() {

  // Usage: WiFi.setPins(CS, IRQ, RST, EN) and EN can be -1 if not specified.
  WiFi.setPins(4, 3, 2, -1); // MAC Address Finder Edit

  Serial.begin(115200);

  nm_bsp_init();
  if (m2m_wifi_download_mode() != M2M_SUCCESS) {
    Serial.println(F("Failed to put the WiFi module in download mode"));
    while (true)
      ;
  }
}

void receivePacket(UartPacket *pkt, uint8_t *payload) {
  // Read command
  uint8_t *p = reinterpret_cast<uint8_t *>(pkt);
  uint16_t l = sizeof(UartPacket);
  while (l > 0) {
    int c = Serial.read();
    if (c == -1)
      continue;
    *p++ = c;
    l--;
  }

  // Convert parameters from network byte order to cpu byte order
  pkt->address = fromNetwork32(pkt->address);
  pkt->arg1 = fromNetwork32(pkt->arg1);
  pkt->payloadLength = fromNetwork16(pkt->payloadLength);

  // Read payload
  l = pkt->payloadLength;
  while (l > 0) {
    int c = Serial.read();
    if (c == -1)
      continue;
    *payload++ = c;
    l--;
  }
}

// Allocated statically so the compiler can tell us
// about the amount of used RAM
static UartPacket pkt;
static uint8_t payload[MAX_PAYLOAD_SIZE];

void loop() {
  receivePacket(&pkt, payload);

  if (pkt.command == CMD_HELLO) {
    if (pkt.address == 0x11223344 && pkt.arg1 == 0x55667788)
      Serial.print("v10000");
  }

  if (pkt.command == CMD_MAX_PAYLOAD_SIZE) {
    uint16_t res = toNetwork16(MAX_PAYLOAD_SIZE);
    Serial.write(reinterpret_cast<uint8_t *>(&res), sizeof(res));
  }

  if (pkt.command == CMD_READ_FLASH) {
    uint32_t address = pkt.address;
    uint32_t len = pkt.arg1;
    if (spi_flash_read(payload, address, len) != M2M_SUCCESS) {
      Serial.println("ER");
    } else {
      Serial.write(payload, len);
      Serial.print("OK");
    }
  }

  if (pkt.command == CMD_WRITE_FLASH) {
    uint32_t address = pkt.address;
    uint32_t len = pkt.payloadLength;
    if (spi_flash_write(payload, address, len) != M2M_SUCCESS) {
      Serial.print("ER");
    } else {
      Serial.print("OK");
    }
  }

  if (pkt.command == CMD_ERASE_FLASH) {
    uint32_t address = pkt.address;
    uint32_t len = pkt.arg1;
    if (spi_flash_erase(address, len) != M2M_SUCCESS) {
      Serial.print("ER");
    } else {
      Serial.print("OK");
    }
  }
}
